fredzo/SarsatJRX/SarsatJRX-code/src/Beacon.cpp

#include "Beacon.h"
#include "Util.h"

// 21 bits BCH polynomial
#define BCH_21_POLYNOMIAL   0b1001101101100111100011UL 
#define BCH_21_POLY_LENGTH  22
// 12 bits BCH polynomial
#define BCH_12_POLYNOMIAL   0b1010100111001UL
#define BCH_12_POLY_LENGTH  13

// User
const Beacon::Protocol Beacon::Protocol::USER_EPIRB_MARITIME(Beacon::Protocol::Type::USER);
const Beacon::Protocol Beacon::Protocol::USER_EPIRB_RADIO(Beacon::Protocol::Type::USER);
const Beacon::Protocol Beacon::Protocol::USER_ELT(Beacon::Protocol::Type::USER);
const Beacon::Protocol Beacon::Protocol::USER_SERIAL(Beacon::Protocol::Type::USER);
const Beacon::Protocol Beacon::Protocol::USER_TEST(Beacon::Protocol::Type::USER);
const Beacon::Protocol Beacon::Protocol::USER_ORB(Beacon::Protocol::Type::USER);
const Beacon::Protocol Beacon::Protocol::USER_NAT(Beacon::Protocol::Type::USER);
const Beacon::Protocol Beacon::Protocol::USER_2G(Beacon::Protocol::Type::USER);
// Standard
const Beacon::Protocol Beacon::Protocol::STD_EPIRB(Beacon::Protocol::Type::STANDARD_LOCATION);
const Beacon::Protocol Beacon::Protocol::STD_ELT_24(Beacon::Protocol::Type::STANDARD_LOCATION);
const Beacon::Protocol Beacon::Protocol::STD_ELT_SERIAL(Beacon::Protocol::Type::STANDARD_LOCATION);
const Beacon::Protocol Beacon::Protocol::STD_ELT_AIRCRAFT(Beacon::Protocol::Type::STANDARD_LOCATION);
const Beacon::Protocol Beacon::Protocol::STD_EPIRB_SERIAL(Beacon::Protocol::Type::STANDARD_LOCATION);
const Beacon::Protocol Beacon::Protocol::STD_PLB_SERIAL(Beacon::Protocol::Type::STANDARD_LOCATION);
const Beacon::Protocol Beacon::Protocol::STD_SHIP(Beacon::Protocol::Type::STANDARD_LOCATION);
const Beacon::Protocol Beacon::Protocol::STD_TEST(Beacon::Protocol::Type::STANDARD_LOCATION);
// National
const Beacon::Protocol Beacon::Protocol::NAT_ELT(Beacon::Protocol::Type::NATIONAL_LOCATION);
const Beacon::Protocol Beacon::Protocol::NAT_EPIRB(Beacon::Protocol::Type::NATIONAL_LOCATION);
const Beacon::Protocol Beacon::Protocol::NAT_PLB(Beacon::Protocol::Type::NATIONAL_LOCATION);
const Beacon::Protocol Beacon::Protocol::NAT_TEST(Beacon::Protocol::Type::NATIONAL_LOCATION);
// RLS / ELT / Spare
const Beacon::Protocol Beacon::Protocol::RLS(Beacon::Protocol::Type::RLS_LOCATION);
const Beacon::Protocol Beacon::Protocol::ELT_DT(Beacon::Protocol::Type::ELT_DT_LOCATION);
const Beacon::Protocol Beacon::Protocol::SPARE(Beacon::Protocol::Type::SPARE);
const Beacon::Protocol Beacon::Protocol::UNKNOWN(Beacon::Protocol::Type::UNKNOWN);


String Beacon::Protocol::getTypeName(bool longFrame) const
{
    switch (type)
    {
        case Type::STANDARD_LOCATION:
            return F("Standard Protocol");
            break;
        case Type::NATIONAL_LOCATION:
            return F("National Protocol");
            break;
        case Type::RLS_LOCATION:
            return F("RLS");
            break;
        case Type::ELT_DT_LOCATION :
            return F("ELT(DT)");
            break;
        case Type::USER:
            return longFrame ? F("User Location Protocol") : F("User Protocol");
            break;
        case Type::SPARE:
            return F("Spare Protocol");
            break;
        case Type::UNKNOWN :
        default:
            return F("Unknown Protocol");
    }
}

uint64_t getBits(byte *data, int startBit, int endBit)
{
    uint64_t result = 0;
    // 0 bases bit count
    startBit--;
    int numBits = endBit - startBit;

    // get a pointer to the starting byte...
    const byte *pData = &(data[startBit / 8]);
    byte b = *pData;

    // calculate the starting bit within that byte...
    int bitOffset = 7 - (startBit % 8);

    // iterate for the desired number of bits...
    for(int i = 0; i < numBits; ++i)
    {
        // make room for the next bit...
        result <<= 1;
        // copy the bit...
        result |= ((b >> bitOffset) & 0x01);
        // reached the end of the current byte?
        if (--bitOffset < 0)
        {
            b = *(++pData); // go to the next byte...
            bitOffset = 7; // restart at the first bit in that byte...
        }
    }

    // all done...
    return result;
}

uint64_t computeBCH(byte* frame, int startBit, int endBit, unsigned long poly, int polyLength)
{   // Length of data to be checked (not including the BCH code)
    int dataLength = endBit-startBit+1;
    // Total lengh (including the BCH code that will be padded to zeros (BCH code length is polyLengh-1))
    int totalLength = dataLength+polyLength-1;
    // Start with the first polyLength bits
    uint64_t result = getBits(frame, startBit,startBit+polyLength-1);
#ifdef DEBUG_BCH    
    Serial.println("BCH calculation :");
    Serial.println((unsigned long)result,2);
#endif
    for (int i = polyLength; i <= totalLength; i++) 
    {   // Iterate on each bit after the first polyLength batch
        bool firstBit = result >> (polyLength-1);
#ifdef DEBUG_BCH    
        Serial.print("First bit :");
        Serial.println(firstBit,2);
#endif
        if(firstBit)
        {   // We have a leading 1 => xor the result with the poly
            result = result^poly;
#ifdef DEBUG_BCH    
            for(int j = 0; j < i-polyLength; j++) Serial.print(" ");
            Serial.println((unsigned long)result,2);
#endif
        }
        if(i<totalLength)
        {   // Move to next bit
            result = result << 1;
#ifdef DEBUG_BCH    
            for(int j = 0; j < i-polyLength; j++) Serial.print(" ");
            Serial.println((unsigned long)result,2);
#endif
            if(i<dataLength)
            {   // Append next bit
                result |= getBits(frame,startBit+i,startBit+i);
#ifdef DEBUG_BCH    
                for(int j = 0; j < i-polyLength; j++) Serial.print(" ");
                Serial.println((unsigned long)result,2);
#endif
            } // else : 0 padding after data length
        }
    }
    return result;
}

uint64_t computeBCH1(byte* frame)
{
    return computeBCH(frame,25,85,BCH_21_POLYNOMIAL,BCH_21_POLY_LENGTH);
}

uint64_t computeBCH2(byte* frame)
{
    return computeBCH(frame,107,132,BCH_12_POLYNOMIAL,BCH_12_POLY_LENGTH);
}

/**
 * Flip the specified bit in this beacon's data
 */
void Beacon::flipBit(int bit) {
    int byteIdx = (bit - 1) / 8;
    int bitIdx = 7 - ((bit - 1) % 8);
    frame[byteIdx] ^= (1 << bitIdx);
}

/**
 * Single bit error correction to match BCH1 or BCH2 code
 */
void Beacon::simpleCorrection(bool isBCH1) {
    for (int i = (isBCH1 ? 25 : 107); i <= (isBCH1 ? 85 : 132); i++) {
        flipBit(i);
        if ((isBCH1 ? (computeBCH1(frame) == bch1) : (computeBCH2(frame) == bch2))) {
            if (isBCH1) {
                computedBch1 = bch1;
                bch1Corrected = true;
            } else {
                computedBch2 = bch2;
                bch2Corrected = true;
            }
            break;
        }
        flipBit(i);  // Restore bit value
    }
}



Beacon::Beacon(volatile byte frameBuffer[], Rtc::Date date)
{   // Get a local copy of the original frame
    memcpy(frame,(const void*)frameBuffer,SIZE);
    Beacon::date = date;
    parseFrame();
}

String Beacon::getFrameTitle()
{
    if (frameMode == Beacon::FrameMode::SELF_TEST) 
    {  // Self-test message frame synchronisation byte
        return F("Self-test 406");
    }
    else if (frameMode == Beacon::FrameMode::NORMAL) 
    {   // Normal message frame synchronisation byte
        if(protocol == &Protocol::USER_SERIAL)
        {
            return F("Serial 406");
        }
        else if(protocol == &Protocol::USER_TEST)
        {
            return F("User Test 406");
        }
        else if(protocol == &Protocol::USER_ORB)
        {
            return F("Orbitography 406");
        }
        else if(protocol == &Protocol::USER_NAT)
        {
            return F("National 406");
        }
        else if(protocol == &Protocol::STD_TEST)
        {
            return F("Test Std. 406");
        }
        else if(protocol == &Protocol::NAT_TEST)
        {
            return F("Test Nat. 406");
        }
        else if(protocol == &Protocol::SPARE)
        {
            return F("Spare 406");
        }
        else
        {
            return F("Distress 406");
        }
    }
    else
    {   // Unknown frame format
        return F("Unknown 406");
    }
}

String Beacon::getProtocolName()
{
    return protocol->getTypeName(longFrame);
}

String Beacon::getProtocolDesciption()
{
    // User
    if(protocol == &Protocol::USER_EPIRB_MARITIME)
    {
        return F("EPIRB - Maritime");
    }
    else if(protocol == &Protocol::USER_EPIRB_RADIO)
    {
        return F("EPIRB - Radio Call Sign");
    }
    else if(protocol == &Protocol::USER_ELT)
    {
        return F("ELT - Aviation");
    }
    else if(protocol == &Protocol::USER_SERIAL)
    {
        return F("Serial User Protocol");
    }
    else if(protocol == &Protocol::USER_TEST)
    {
        return F("Test User Protocol");
    }
    else if(protocol == &Protocol::USER_ORB)
    {
        return F("Orbitography Protocol");
    }
    else if(protocol == &Protocol::USER_NAT)
    {
        return F("National User Protocol");
    }
    else if(protocol == &Protocol::USER_2G)
    {
        return F("2nd Generation Beacons");
    }
    // Standard
    else if(protocol == &Protocol::STD_EPIRB)
    {
        return F("EPIRB - MMSI / Location");
    }
    else if(protocol == &Protocol::STD_ELT_24)
    {
        return F("ELT-24-bit Address / Location");
    }
    else if(protocol == &Protocol::STD_ELT_SERIAL)
    {
        return F("ELT Serial Location");
    }
    else if(protocol == &Protocol::STD_ELT_AIRCRAFT)
    {
        return F("ELT Serial Aircradt Location");
    }
    else if(protocol == &Protocol::STD_EPIRB_SERIAL)
    {
        return F("EPIRB Serial Location");
    }
    else if(protocol == &Protocol::STD_PLB_SERIAL)
    {
        return F("PLB Serial Location");
    }
    else if(protocol == &Protocol::STD_SHIP)
    {
        return F("Ship Security Location");
    }
    else if(protocol == &Protocol::STD_TEST)
    {
        return F("Test Standard Location");
    }
    // National
    else if(protocol == &Protocol::NAT_ELT)
    {
        return F("ELT National Location");
    }
    else if(protocol == &Protocol::NAT_EPIRB)
    {
        return F("EPIRB National Location");
    }
    else if(protocol == &Protocol::NAT_PLB)
    {
        return F("PLB National Location");
    }
    else if(protocol == &Protocol::NAT_TEST)
    {
        return F("Test National Location");
    }
    // RLS / ELT / Spare
    else if(protocol == &Protocol::RLS)
    {
        return F("RLS Location Protocol");
    }
    else if(protocol == &Protocol::ELT_DT)
    {
        return F("ELT(DT) Location Protocol");
    }
    else if(protocol == &Protocol::SPARE)
    {
        return F("Spare");
    }
    else
    {
        return F("Unknown Protocol");
    }
}

bool Beacon::hasMainLocatingDevice()
{
    return (mainLocatingDevice != MainLocatingDevice::UNDEFINED);
}

String Beacon::getMainLocatingDeviceName()
{
    switch (mainLocatingDevice)
    {
        case MainLocatingDevice::EXTERNAL_NAV :
            return F("Exernal");
            break;
        case MainLocatingDevice::INTERNAL_NAV :
            return F("Internal");
            break;
        default:
            return F("Undefined");
    }
}

bool Beacon::hasAuxLocatingDevice()
{
    return (auxLocatingDevice != AuxLocatingDevice::UNDEFINED);
}

String Beacon::getAuxLocatingDeviceName()
{
    switch (auxLocatingDevice)
    {
        case AuxLocatingDevice::NONE :
            return F("No device");
            break;
        case AuxLocatingDevice::NONE_OR_OTHER :
            return F("Other or no device");
            break;
        case AuxLocatingDevice::OTHER :
            return F("Other device");
            break;
        case AuxLocatingDevice::MHZ121_5 :
            return F("121.5 MHz");
            break;
        case AuxLocatingDevice::SART :
            return F("Maritime locating: 9 GHz SART");
            break;
        default:
            return F("Undefined");
    }
}

void Beacon::parseProtocol()
{
    protocolFlag = getBits(frame,26,26); // protocol flag : bit 26
    if(protocolFlag)
    {   // User protocol
        protocolCode = getBits(frame,37,39);  // protocol code : bits 37-39
    }
    else
    {   // Other protocols
        protocolCode = getBits(frame,37,40);    // protocol code     bits 37-40
    }

    if(!longFrame || protocolFlag == 1) 
    {   // User protocol (3 bits)
        switch(protocolCode)
        {
            case 0b000 :
                protocol = &Protocol::USER_ORB;
                break;
            case 0b001 :
                protocol = &Protocol::USER_ELT;
                break;
            case 0b010 :
                protocol = &Protocol::USER_EPIRB_MARITIME;
                isMaritime = true;
                break;
            case 0b011 :
                protocol = &Protocol::USER_SERIAL;
                break;
            case 0b100 :
                protocol = &Protocol::USER_NAT;
                break;
            case 0b101 :
                protocol = &Protocol::USER_2G;
                break;
            case 0b110 :
                protocol = &Protocol::USER_EPIRB_RADIO;
                isMaritime = true;
                break;
            case 0b111 :
                protocol = &Protocol::USER_TEST;
                break;
            default:
                protocol = &Protocol::UNKNOWN;
        }
    }
    else
    {   // Other protocols (4 bits)
        switch(protocolCode)
        {
            case 0b0000 :
            case 0b0001 :
                protocol = &Protocol::SPARE;
                break;
            case 0b0010 :
                protocol = &Protocol::STD_EPIRB;
                break;
            case 0b0011 :
                protocol = &Protocol::STD_ELT_24;
                break;
            case 0b0100 :
                protocol = &Protocol::STD_ELT_SERIAL;
                break;
            case 0b0101 :
                protocol = &Protocol::STD_ELT_AIRCRAFT;
                break;
            case 0b0110 :
                protocol = &Protocol::STD_EPIRB_SERIAL;
                break;
            case 0b0111 :
                protocol = &Protocol::STD_PLB_SERIAL;
                break;
            case 0b1000 :
                protocol = &Protocol::NAT_ELT;
                break;
            case 0b1001 :
                protocol = &Protocol::ELT_DT;
                break;
            case 0b1010 :
                protocol = &Protocol::NAT_EPIRB;
                break;
            case 0b1011 :
                protocol = &Protocol::NAT_PLB;
                break;
            case 0b1100 :
                protocol = &Protocol::STD_SHIP;
                break;
            case 0b1101 :
                protocol = &Protocol::RLS;
                break;
            case 0b1110 :
                protocol = &Protocol::STD_TEST;
                break;
            case 0b1111 :
                protocol = &Protocol::NAT_TEST;
                break;
            default:
                protocol = &Protocol::UNKNOWN;
        }
    }
}

void Beacon::setSerialNumber(uint32_t serial)
{
        serialNumber  = String(serial, HEX);
        serialNumber.toUpperCase();
        serialNumber = String(serial,DEC) + " (0x" + serialNumber + ")";
}

void Beacon::parseAdditionalData()
{
    hasAdditionalData = false;
    hasSerialNumber = false;
    if(protocolFlag)
    {   // User protocols
        if(protocolCode == 0b011)
        {   // Serial user
            byte serialUserProtocol = getBits(frame,40, 42);
            hasAdditionalData = true;
            switch(serialUserProtocol)
            {
                case 0b000: additionalData  = F("ELTs/serial identification number"); break;
                case 0b001: additionalData  = F("ELTs/aircraft operator & serial #"); break;
                case 0b010: additionalData  = F("Float free EPIRBs/serial #"); isMaritime = true; break;
                case 0b011: additionalData  = F("ELTs with aircraft 24-bit address"); break;
                case 0b100: additionalData  = F("Non float free EPIRBs/serial #"); break;
                case 0b110: additionalData  = F("PLBs/serial identification #"); break;
                default : hasAdditionalData = false;
            }
            hasSerialNumber = true;
            setSerialNumber((serialUserProtocol == 0b011) ? getBits(frame, 44, 67) : (serialUserProtocol == 0b001) ? getBits(frame, 62, 73) : getBits(frame, 44, 63));
        }
        if (!longFrame) {
            hasEmergency = getBits(frame, 107, 107);
            if (hasEmergency) {
                isAutoamticEmergency = getBits(frame, 108, 108);
                if (isMaritime) {
                    uint8_t emmergency = getBits(frame, 109, 112);
                    switch (emmergency) {
                        case 0b0001: emergencyType = F("Fire/explosion"); break;
                        case 0b0010: emergencyType = F("Flooding"); break;
                        case 0b0011: emergencyType = F("Collision"); break;
                        case 0b0100: emergencyType = F("Grounding"); break;
                        case 0b0101: emergencyType = F("Danger of capsizing"); break;
                        case 0b0110: emergencyType = F("Sinking"); break;
                        case 0b0111: emergencyType = F("Disabled and adrift"); break;
                        case 0b1000: emergencyType = F("Abandoning ship"); break;
                        default:     emergencyType = F("Unspecified distress");
                    }
                } else {
                    bool fire = getBits(frame, 109, 109);
                    bool med = getBits(frame, 110, 110);
                    bool disabled = getBits(frame, 111, 111);
                    if (fire) emergencyType = "Fire";
                    if (med) {
                        if (fire) emergencyType += "+";
                        emergencyType += "Medical";
                    }
                    if (disabled) {
                        if (fire || med) emergencyType += "+";
                        emergencyType += "Disabled";
                    }
                }
            }
        }
    }
    else if (longFrame)
    {   // Long frame other than User Protocol
        switch(protocolCode)
        {
            case 0b0010 :
                {
                hasSerialNumber = true;
                setSerialNumber(getBits(frame,61,64));
                }
                break;
            case 0b1100 :
                {
                hasAdditionalData = true;
                uint32_t mmsi = getBits(frame,41,60);
                additionalData = "MMSI=" + String(mmsi, HEX) + " MID=" + mmsi;
                additionalData.toUpperCase();
                }
                break;
            case 0b0011 :
                {
                hasAdditionalData = true;
                hasSerialNumber = true;
                setSerialNumber(getBits(frame,41,64));
                additionalData = "24 bits aircraft address";
                }
                break;
            case 0b0100 :
            case 0b0110 :
            case 0b0111 :
                {
                hasAdditionalData = true;
                hasSerialNumber = true;
                uint32_t csTaNumber = getBits(frame,41, 50);
                additionalData = "C/S TA #=" + String(csTaNumber, DEC);
                setSerialNumber(getBits(frame,51, 64));
                }
                break;
            case 0b0101 :
                { 
                hasAdditionalData = true;
                hasSerialNumber = true;
                uint32_t data = getBits(frame,41, 45); // 1st char
                data = data + 32;
                additionalData = BAUDOT_CODE[data];

                data = getBits(frame,46, 50); // 2nd char
                data = data + 32;
                additionalData = additionalData + BAUDOT_CODE[data];

                data = getBits(frame,51, 55); // 3rd char
                data = data + 32;
                additionalData = additionalData + BAUDOT_CODE[data];

                additionalData = "Op Design.=" + additionalData;

                setSerialNumber(getBits(frame,56, 64));
                }
                break;
            case 0b1000 :
            case 0b1010 :
            case 0b1011 :
            case 0b1111 :
                {
                hasSerialNumber = true;
                hasAdditionalData = true;
                setSerialNumber(getBits(frame,41, 58));
                uint32_t natNum = getBits(frame,127, 132);
                additionalData = "National data=" + String(natNum, DEC);
                }
                break;
        }
    }
}

void Beacon::parseLocatingDevices()
{
    // Main 
    bool mainLocating;
    if(protocol->isStandard() || protocol->isNational())
    {
        mainLocating = getBits(frame,111,111);
        mainLocatingDevice = mainLocating ? MainLocatingDevice::INTERNAL_NAV : MainLocatingDevice::EXTERNAL_NAV;
    }
    else if (protocol->isUser()||protocol->isRls())
    {
        mainLocating = getBits(frame,107,107);
        mainLocatingDevice = mainLocating ? MainLocatingDevice::INTERNAL_NAV : MainLocatingDevice::EXTERNAL_NAV;
    }
    // Aux
    if(protocol->isStandard() || protocol->isNational())
    {
        bool auxLocating = getBits(frame,112,112);
        auxLocatingDevice = auxLocating ? AuxLocatingDevice::MHZ121_5 : AuxLocatingDevice::NONE_OR_OTHER;
    }
    else if (protocol->isRls())
    {
        bool auxLocating = getBits(frame,108,108);
        auxLocatingDevice = auxLocating ? AuxLocatingDevice::MHZ121_5 : AuxLocatingDevice::NONE_OR_OTHER;
    }
    else if (protocol->isUser() && protocolCode != 0b100)
    {   // User protocol with an aux locating device
        byte auxLocating = getBits(frame,84,85);
        switch (auxLocating)
        {
            case 0b00:
                auxLocatingDevice = AuxLocatingDevice::NONE;
                break;
            case 0b01:
                auxLocatingDevice = AuxLocatingDevice::MHZ121_5;
                break;
            case 0b10:
                auxLocatingDevice = AuxLocatingDevice::SART;
                break;
            case 0b11:
                auxLocatingDevice = AuxLocatingDevice::OTHER;
                break;
        }
    }
}

void Beacon::parseFrame()
{
    long latofmin, latofsec, lonofmin, lonofsec;
    bool latoffset, lonoffset;

    longFrame = getBits(frame,25,25);       // frame size : bit 25
    parseProtocol();
    unsigned long countryCode = getBits(frame, 27,36); // country code bit 27-36
    country = Country::getCountry(countryCode);
        
    if (frame[2] == 0xD0) 
    {  // Self-test message frame synchronisation byte
        frameMode = FrameMode::SELF_TEST;
    }
    else if (frame[2] == 0x2F) 
    { // Normal message frame synchronisation byte
        frameMode = FrameMode::NORMAL;
    }
    else
    {
        frameMode = FrameMode::UNKNOWN;
    }

    if (longFrame)
    {
        if(protocol->isUser() && !isOrbito()) 
        {   // User loc protocol long frame (no location for Obitography frame)
            location.latitude.orientation = (frame[13] & 0x10) >> 4;   
            location.latitude.degrees = ((frame[13] & 0x0F) << 3 | (frame[14] & 0xE0) >> 5);
            location.latitude.minutes = (frame[14] & 0x1E) >> 1;
            location.latitude.minutes = (location.latitude.minutes * 4);
            location.longitude.orientation = (frame[14] & 0x01);           
            location.longitude.degrees = (frame[15]);
            location.longitude.minutes = (frame[16] & 0xF0) >> 4;
            location.longitude.minutes = (location.longitude.minutes * 4);
        }
        else if(protocol->isNational())
        {   // Nat loc protocol
            latoffset = (frame[14] & 0x80) >> 7;   // Latitude NAT LOCATION
            location.latitude.orientation = (frame[7] & 0x20) >> 5;   
            location.latitude.degrees = ((frame[7] & 0x1F) << 2 | (frame[8] & 0xC0) >> 6);
            location.latitude.minutes = (frame[8] & 0x3E) >> 1;
            location.latitude.minutes = (location.latitude.minutes * 2);
            latofmin = (frame[14] & 0x60) >> 5;
            latofsec = (frame[14] & 0x1E) >> 1;
            latofsec = (latofsec * 4);
            if (latoffset == 1) 
            {
                location.latitude.minutes += latofmin;
                location.latitude.seconds += latofsec;
            }
            else if (latoffset == 0) 
            {
                location.latitude.minutes -= latofmin;
                if (location.latitude.minutes < 0) 
                {
                    location.latitude.minutes += 60;
                    location.latitude.degrees -= 1;
                }
                location.latitude.seconds -= latofsec;
                if (location.latitude.seconds < 0) 
                {
                    location.latitude.seconds += 60;
                    location.latitude.minutes -= 1;
                }
            }

            lonoffset = (frame[14] & 0x01);
            location.longitude.orientation = (frame[8] & 0x01);           
            location.longitude.degrees = (frame[9]);
            location.longitude.minutes = (frame[10] & 0xF8) >> 3;
            location.longitude.minutes = (location.longitude.minutes * 2);
            lonofmin = (frame[15] & 0xC0) >> 6;
            lonofsec = (frame[15] & 0x3C) >> 2;
            lonofsec = (lonofsec * 4);
            if (lonoffset == 1) 
            {
                location.longitude.minutes += lonofmin;
                location.longitude.seconds += lonofsec;
            }
            else if (lonoffset == 0) 
            {
                location.longitude.minutes -= lonofmin;
                if (location.longitude.minutes < 0) 
                {
                    location.longitude.minutes += 60;
                    location.longitude.degrees -= 1;
                }
                location.longitude.seconds -= lonofsec;
                if (location.longitude.seconds < 0) 
                {
                    location.longitude.seconds += 60;
                    location.longitude.minutes -= 1;
                }
            }
        }
        else if (protocol->isStandard())
        {   //Std loc protocol
            latoffset = (frame[14] & 0x80) >> 7;
            location.latitude.orientation = (frame[8] & 0x80) >> 7; 
            location.latitude.degrees = (frame[8] & 0x7F);
            location.latitude.minutes = (frame[9] & 0xC0) >> 6;
            location.latitude.minutes = (location.latitude.minutes * 15);
            latofmin = (frame[14] & 0x7C) >> 2;
            latofsec = ((frame[14] & 0x03) << 2 | (frame[15] & 0xC0) >> 6);
            latofsec = (latofsec * 4);
            if (latoffset == 1) 
            {
                location.latitude.minutes += latofmin;
                location.latitude.seconds += latofsec;
            }
            else if (latoffset == 0) 
            {
                location.latitude.minutes -= latofmin;
                if (location.latitude.minutes < 0) 
                {
                    location.latitude.minutes += 60;
                    location.latitude.degrees -= 1;
                }
                location.latitude.seconds -= latofsec;
                if (location.latitude.seconds < 0) 
                {
                    location.latitude.seconds += 60;
                    location.latitude.minutes -= 1;
                }
            }
            
            lonoffset = (frame[15] & 0x20) >> 5;  //Longitude STD LOCATION
            location.longitude.orientation = (frame[9] & 0x20) >> 5; 
            location.longitude.degrees = ((frame[9] & 0x1F) << 3 | (frame[10] & 0xE0) >> 5);
            location.longitude.minutes = (frame[10] & 0x18) >> 3;
            location.longitude.minutes = (location.longitude.minutes * 15);
            lonofmin = (frame[15] & 0x1F);
            lonofsec = (frame[16] & 0xF0) >> 4;
            lonofsec = (lonofsec * 4);
            if (lonoffset == 1) 
            {
                location.longitude.minutes += lonofmin;
                location.longitude.seconds += lonofsec;
            }
            else if (lonoffset == 0) 
            {
                location.longitude.minutes -= lonofmin;
                if (location.longitude.minutes < 0) 
                {
                    location.longitude.minutes += 60;
                    location.longitude.degrees -= 1;
                }
                location.longitude.seconds -= lonofsec;
                if (location.longitude.seconds < 0) 
                {
                    location.longitude.seconds += 60;
                    location.longitude.minutes -= 1;
                }
            }
        }
        else if(protocol->isRlsOrElt())
        {   // RLS Location protocol => protocolCode == 0b1101 / ELT(DT) Location protocol => protocolCode == 0b1001
            latoffset = (frame[14] & 0x20) >> 5;
            location.latitude.orientation = (frame[8] & 0x20) >> 5; 
            location.latitude.degrees = ((frame[8] & 0x1F) << 2) | ((frame[9] & 0xC0) >> 6);
            location.latitude.minutes = (frame[9] & 0x20) >> 5;
            location.latitude.minutes = (location.latitude.minutes * 30);
            latofmin = (frame[14] & 0x1E) >> 1;
            latofsec = ((frame[14] & 0x01) << 3 | (frame[15] & 0xE0) >> 5);
            latofsec = (latofsec * 4);
            if (latoffset == 1) 
            {
                location.latitude.minutes += latofmin;
                location.latitude.seconds += latofsec;
            }
            else if (latoffset == 0) 
            {
                location.latitude.minutes -= latofmin;
                if (location.latitude.minutes < 0) 
                {
                    location.latitude.minutes += 60;
                    location.latitude.degrees -= 1;
                }
                location.latitude.seconds -= latofsec;
                if (location.latitude.seconds < 0) 
                {
                    location.latitude.seconds += 60;
                    location.latitude.minutes -= 1;
                }
            }
            
            lonoffset = (frame[15] & 0x10) >> 4;
            location.longitude.orientation = (frame[9] & 0x10) >> 4; 
            location.longitude.degrees = ((frame[9] & 0x0F) << 4 | (frame[10] & 0xF0) >> 4);
            location.longitude.minutes = (frame[10] & 0x08) >> 3;
            location.longitude.minutes = (location.longitude.minutes * 30);
            lonofmin = (frame[15] & 0x0F);
            lonofsec = (frame[16] & 0xF0) >> 4;
            lonofsec = (lonofsec * 4);
            if (lonoffset == 1) 
            {
                location.longitude.minutes += lonofmin;
                location.longitude.seconds += lonofsec;
            }
            else if (lonoffset == 0) 
            {
                location.longitude.minutes -= lonofmin;
                if (location.longitude.minutes < 0) 
                {
                    location.longitude.minutes += 60;
                    location.longitude.degrees -= 1;
                }
                location.longitude.seconds -= lonofsec;
                if (location.longitude.seconds < 0) 
                {
                    location.longitude.seconds += 60;
                    location.longitude.minutes -= 1;
                }
            }
        }
    }

    // Parse additional data
    parseAdditionalData();

    // Parse locating device information
    parseLocatingDevices();

    // Hex id from bits 26-85
    identifier = getBits(frame,26,85);

    uint32_t hexIdHigh = (uint32_t)(identifier >> 32);
    uint32_t hexIdLow = (uint32_t)identifier;

    if (protocol->isStandard()) {
        // default value of bits 65 to 74 = 0 111111111 / default value of bits 75 to 85 = 0 1111111111
        hexIdLow &= 0b11111111111000000000000000000000;
        hexIdLow |= 0b00000000000011111111101111111111;
    } else if (protocol->isNational()) {
        // default value of bits 59 to 71 = 0 1111111 00000 / default value of bits 72 to 85 = 0 11111111 00000
        hexIdLow &= 0b11111000000000000000000000000000;
        hexIdLow |= 0b00000011111110000001111111100000;
    } else if (protocol->isRlsOrElt()) {
        // default value of bits 67 to 75 = 0 11111111 / default value of bits 76 to 85 = 0 111111111
        hexIdLow &= 0b11111111111110000000000000000000;
        hexIdLow |= 0b00000000000000111111110111111111;
    }
    // Format HexId to string
    char buffer[32];
    snprintf(buffer,sizeof(buffer),"%07lX%08lX",hexIdHigh,hexIdLow);
    hexId = String(buffer);

    // Check for Empty frame
    if(isOrbito()&&!longFrame)
    {
        isEmpty = true;
        for (size_t i = 3; i < SIZE; i++) 
        {
            if (frame[i] != 0) 
            {
                isEmpty = false;
                break;
            }
        }
    }
    else
    {
        isEmpty = false;
    }

    // Actual and computed BCH1 and BCH2 values
    bch1 = getBits(frame,86,106);
    computedBch1 = computeBCH1(frame);
    // Try and correct single bit error on  BCH1 (bits 25-85)
    if (computedBch1 != bch1) {
        simpleCorrection(true);
    }

    // Special handing of Orbitography Protocol that has no BCH2 error correction code
    hasBch2 = longFrame && !isOrbito();
    if(hasBch2)
    {
        bch2 = getBits(frame,133,144);
        computedBch2 = computeBCH2(frame);
        // Try and correct single bit error on  BCH2 (bits 107 - 132)
        if (computedBch2 != bch2) {
            simpleCorrection(false);
        }
    }
    static bool isCorrecting = false;
    // If BCH1 or BCH2 has been corrected, we need to parse frame again to update beacon properties
    if (!isCorrecting && (bch1Corrected || bch2Corrected)) {
        // Prevent recursion
        isCorrecting = true;
        parseFrame();
        isCorrecting = false;
    }
}

bool Beacon::isBch1Valid()
{
    return (bch1 == computedBch1);
}

bool Beacon::isBch2Valid()
{
    return (bch2 == computedBch2);
}

bool Beacon::isFrameValid()
{
    return isBch1Valid() && ((!hasBch2)||isBch2Valid()) && (!isEmpty);
}

bool Beacon::isOrbito()
{
    return (protocol == &Protocol::USER_ORB);    
}

String Beacon::toKvpString()
{
    String result;
    result+="date="+date.getDateString()+"\n";
    result+="time="+date.getTimeString()+"\n";
    // Frame title
    result+="title="+getFrameTitle()+"\n";
    // Protocol name
    result+="protocol="+getProtocolName()+"\n";
    // Protocol description
    result+="protocolDesc="+getProtocolDesciption()+"\n";
    // Protocol additional data
    if(hasAdditionalData)
    {   // Additionnal protocol data
        result+="protocolAddData="+additionalData+"\n";
    }

    // Location
    // Country
    result+="country="+country.toString()+"\n";
    // Coordinates
    if(!location.isUnknown())
    {
        result+="lat="+String(location.latitude.getFloatValue(),6)+"\n";
        result+="lon="+String(location.longitude.getFloatValue(),6)+"\n";
    }
    // Control codes
    result+="bch1=" + (isBch1Valid() ? (bch1Corrected ? String("co") : String("ok")) : String("ko")) +"\n";
    if(longFrame && hasBch2) 
    {   // No second proteced field in short frames
        result+="bch2=" + (isBch2Valid() ? (bch2Corrected ? String("co") : String("ok")) : String("ko")) +"\n";
    }

    // Hex ID
    result+="hexId=" + hexId +"\n";

    // Serial #
    if(hasSerialNumber)
    { // Serial number
        result+="serial=" + serialNumber +"\n";
    }

    // Emergency
    if(hasEmergency)
    { // Serial number
        result+="emergency=" + emergencyType +"\n";
        result+="emergencyMode=" + (isAutoamticEmergency ? String("auto") : String("manual")) +"\n";
    }

    // Location devices
    if(hasMainLocatingDevice())
    { // Main locating device
        result+="mainDevice=" + getMainLocatingDeviceName() +"\n";
    }

    if(hasAuxLocatingDevice())
    {   // Auxiliary locating device
        result+="auxDevice=" + getAuxLocatingDeviceName() +"\n";
    }

    // Data
    result+="data=" + hexString(false) +"\n";
    return result;
}

String Beacon::hexString(bool withHeader)
{
    return toHexString(frame, false, (withHeader ? 0 : 3), (longFrame ? 18 : 14));
}
