fredzo/SarsatJRX/SarsatJRX-code/src/Power.cpp

#include "Power.h"
#include <SarsatJRXConf.h>
#include <Util.h>

#define MAX_BATTERY_VOLTAGE_DOWN    4.1
#define MAX_BATTERY_VOLTAGE_UP      4.2
#define POWER_SAMPLE_PERIOD         200  // 200ms
#define POWER_UPDATE_PERIOD         1000 // 1s
#define CHARGE_SAMPLE_PERIOD        1    // 1 ms: depending on charger chip mode, fickering is charge pin going low for around 1ms every 10 to 50 ms 
#define CHARGE_SAMPLE_COUNT         100  // Wait for 100 consecutive samples with same value to validate charge state
#define CHARGE_BATTERY_OFF_COUNT    10   // Wait for 10 state changes to determine if battery is off

// Static members
Power *Power::powerInstance = nullptr;


void Power::powerInit()
{
  pinMode(BATTERY_ADC_PIN, ANALOG);      // Battery level pin
  pinMode(CHARGE_INPUT_PIN, INPUT_PULLUP);      // Charge status pin
}


/**
 * @brief Returns actual VCC value
 * 
 * @return VCC value
 */
float Power::getVccValue() {
    changed = false;
    return powerValue;
}

/**
 * @brief Read VCC value into the provided char* with the format "x.xx"
 * 
 * @return The VCC string value
 */
String Power::getVccStringValue()
{   /* 6 is mininum width, 4 is precision; float value is copied onto angleStr */
    char buffer[8];
    dtostrf(getVccValue(), 3, 2, buffer);
    return (String(buffer) + "V");
}

/**
 * @brief Read raw VCC value into the provided char* with the format "x.xx"
 * 
 * @return The VCC string value
 */
String Power::getRawVccStringValue()
{   /* 6 is mininum width, 4 is precision; float value is copied onto angleStr */
    char buffer[8];
    dtostrf(getRawVccValue(), 3, 2, buffer);
    return (String(buffer) + "V");
}

Power::PowerState Power::getPowerState()
{
    return state;
}

String Power::getPowerStateString()
{
    String result;
    switch (getPowerState())
    {
    case PowerState::FULL :
        result = "Battery full";
        break;
    case PowerState::ON_BATTERY :
        result = "On Battery";
        break;
    case PowerState::NO_BATTERY :
        result = "Battery switch off";
        break;
    case PowerState::CHARGING :
    default:
        result = "Charging";
        break;
    }
    return result;
}

bool Power::hasPowerStateChanged()
{
    bool result = powerStateChanged;
    powerStateChanged = false;
    return result;
}


int Power::getBatteryPercentage()
{
    return batteryPercentage;
}

// For rolling average
void Power::addPowerSample(float newVoltage) 
{
    if (voltageCount < BATTERY_BUFFER_SIZE) 
    {
        // Initial filling
        voltageBuffer[voltageIndex] = newVoltage;
        voltageSum += newVoltage;
        voltageCount++;
    } 
    else 
    {   // Buffer full : remove old value, add new
        float oldVoltage = voltageBuffer[voltageIndex];
        voltageBuffer[voltageIndex] = newVoltage;
        voltageSum += newVoltage - oldVoltage;
    }
    voltageIndex = (voltageIndex + 1) % BATTERY_BUFFER_SIZE;
}

// Get rolling average
float Power::getAveragePowerValue(void) 
{
    if (voltageCount == 0) return 0.0f;
    return voltageSum / voltageCount;
}

// Power task processing
void Power::handleTask()
{   // This task is in charge of updating power value and power state
    unsigned long now = millis();
    if(now - lastPowerSampleTime > POWER_SAMPLE_PERIOD)
    {   // Time to make a new sample
        lastPowerSampleTime = now;
        uint32_t v = analogReadMilliVolts(BATTERY_ADC_PIN);
        rawPowerValue = (((float)v)*2.0/1000.0);

        // Compute rolling average
        addPowerSample(rawPowerValue);
        float newValue = getAveragePowerValue();
        // Simu
        /* newValue = powerValue - 0.05;
        if(newValue < 3.3)
        {
            newValue = 4.3;
        }*/
        // Simu
        if((powerValue == 0) || (now - lastPowerUpdateTime > POWER_UPDATE_PERIOD))
        {
            lastPowerUpdateTime = now;
            if(abs(newValue - powerValue) > 0.01)
            {   // Filter small value changes
                powerValue = newValue;
                int newBatteryPercentage = voltageToPercent(powerValue,3.0f,4.0f);
                if(abs(newBatteryPercentage - batteryPercentage) > 5)
                {   // Round to nearest 5
                    batteryPercentage = ((newBatteryPercentage + 2) / 5) * 5;
                }
                changed = true;
            }
        }
    }
    if(now - lastChargeSampleTime > CHARGE_SAMPLE_PERIOD)
    {   // Time to make a new sample
        lastChargeSampleTime = now;
        int newValue = digitalRead(CHARGE_INPUT_PIN);
        if(newValue == lastChargeValue)
        {   // Is pin value stable (we want to detect the fickering state of the charging led of the TP4054 that refects no battery is connected (battery switch is off))
            if((chargeValueCount < CHARGE_SAMPLE_COUNT) || changed) // If power value changed, we may need to update state too
            {   // Count consecutive values
                chargeValueCount++;
                if(chargeValueCount >= CHARGE_SAMPLE_COUNT)
                {   // Update power state if value is stable
                    PowerState newState;
                    if(lastChargeValue)
                    {   // Led off (pin high) => either full or on battery
                        if(powerValue >= MAX_BATTERY_VOLTAGE_UP)
                        {
                            newState = PowerState::FULL;
                        }
                        else
                        {
                            if(powerValue >= MAX_BATTERY_VOLTAGE_DOWN && state == PowerState::CHARGING)
                            {   // Previous state was charging => must be full now
                                newState = PowerState::FULL;
                            }
                            else
                            {
                                newState = PowerState::ON_BATTERY;
                            }
                        }
                    }
                    else
                    {   // Charging
                        newState = PowerState::CHARGING;
                    }
                    if(newState != state)
                    {
                        state = newState;
                        changed = true;
                        powerStateChanged = true;
                    }
                }
            }
        }
        else
        {   // Led is flickering => no battery connected
            chargeValueCount = 0;
            if(state != PowerState::NO_BATTERY)
            {
                if(chargeSampleCount >= CHARGE_BATTERY_OFF_COUNT)
                {
                    state = PowerState::NO_BATTERY;
                    powerStateChanged = true;
                    changed = true;
                    chargeSampleCount = 0;
                }
                else
                {
                    chargeSampleCount++;
                }
            }
            lastChargeValue = newValue;
        }
    }
}
