fredzo/SarsatJRX/SarsatJRX-code/src/SoundManager.h

#ifndef MUSIC_MANAGER_H
#define MUSIC_MANAGER_H

#include <SarsatJRXConf.h>
#include <melody_player.h>
#include <melody_factory.h>


class SoundManager
{
    public :

        static SoundManager *getSoundManager()
        {
            if (soundManagerInstance == nullptr) {
                soundManagerInstance = new SoundManager();
            }
            return soundManagerInstance;
        }

        void init();

        void setVolume(byte volume);

        void playFrameSound(bool error);

        void playInvalidFrameSound();

        void playFilteredFrameSound();

        void playCountDownLowSound();

        void playCountDownHighSound();

        void playTouchSound();

        void unmute();


    private :

        MelodyPlayer* player;

        Melody frameOkSound;
        Melody frameKoSound;
        Melody frameInvalidSound;
        Melody frameFilteredSound;
        Melody countDownLowSound;
        Melody countDownHighSound;
        Melody touchSound;


        SoundManager()
        {   // Uses channel 4 since channel 0 is used for LCD Backlight
            player = new MelodyPlayer(BUZZER_PIN,4,LOW);
        };

        ~SoundManager()
        {
            delete player;
        };

        static SoundManager *soundManagerInstance;
};

#endif 
