fredzo/SarsatJRX/SarsatJRX-code/src/Util.cpp

#include "Util.h"


#ifdef DEBUG_RAM
uint32_t freeRam()
{
  return ESP.getFreeHeap();
}
void logFreeRam()
{
   Serial.printf("Free ram : %d\n",ESP.getFreeHeap());
}
#endif


/**
 * @brief Convert the provided frame to it's Hex String representation
 * 
 * @param frame the frame to convert
 * @param withSpace true if bytes should be seperated by spaces
 * @param start start byte
 * @param end end byte
 * @return String 
 */
String toHexString(volatile byte* frame, bool withSpace, int start, int end)
{
  char buffer[4];
  String result = "";
  for ( byte i = start; i < end; i++) 
  {
    snprintf(buffer,sizeof(buffer), "%02X", frame[i]);
    if(withSpace && i>start) 
    {
      result += " ";
    }
    result += buffer;
  }
  return result;
}

/**
 * @brief Read the provided hexString and store the content in the buffer
 * 
 * @param buffer the buffer to store the converted hex bytes into (the size must match the hex string size)
 * @param hexString the hex string to read
 */
void readHexString(volatile byte* buffer, String hexString) 
{
  for (unsigned int i = 0; i < hexString.length(); i += 2) {
    String byteString = hexString.substring(i, i+2);
    byte b = (byte)strtol(byteString.c_str(), NULL, 16);
    buffer[i/2]=b;
  }
}

String formatMemoryValue(uint32_t value, bool showByteValue)
{
  char buffer[64];
  uint32_t kbValue = value / 1024;
  if(showByteValue)
  {
    snprintf(buffer,sizeof(buffer),"%'d kB (%'d bytes)",kbValue,value);
  }
  else
  {
    snprintf(buffer,sizeof(buffer),"%'d kB",kbValue);
  }
  return String(buffer);
}

String formatFrequencyValue(uint32_t value)
{
  return (String(value) + " Mhz");
}

String formatDbmValue(int8_t value)
{
  return (String(value) + " dBm");
}

String formatHzFrequencyValue(uint32_t value)
{
  return (String(value/1000000) + " Mhz");
}

String formatSketchInformation(uint32_t size, String md5)
{
  int md5Length = md5.length();
  //Serial.println(md5);
  if(md5Length > 16)
  {
    md5 = md5.substring(0,8) + "..." + md5.substring(md5Length-8,md5Length);
    //Serial.println(md5);
  }
  return formatMemoryValue(size,false) + " (MD5=" + md5 + ")";
}

void formatBeaconFileName(char* buffer, size_t size, String name)
{
  snprintf(buffer,size,"%s/%s/%s - %s:%s:%s",name.substring(0,2),name.substring(2,4),name.substring(4,8),name.substring(9,11),name.substring(11,13),name.substring(13,15));
}

Rtc::Date parseBeaconFileName(const char* fileName)
{
  String name = String(fileName);
  Rtc::Date result;
  result.day = atoi(name.substring(0,2).c_str());
  result.month = atoi(name.substring(2,4).c_str());
  result.year = atoi(name.substring(4,8).c_str());
  result.hour = atoi(name.substring(9,11).c_str());
  result.minute = atoi(name.substring(11,13).c_str());
  result.second = atoi(name.substring(13,15).c_str());
  return result;
}

void formatFrequencyItem(char* buffer, size_t size, int index, float frequency, bool on)
{
    snprintf(buffer,size,"(%c) %d- %3.4f MHz",on ? '*' : ' ', index+1, frequency);
}

typedef struct {
    float voltage;
    uint8_t percent;
} voltageMap_t;

// Simplified battery discharge curve
typedef struct {
    float relVoltage;   // Relative voltage (from 0.0 to 1.0)
    uint8_t percent;
} battery_point_t;

// Normalized discharge curve
static const battery_point_t batteryCurve[] = {
    {1.00, 100},
    {0.98,  95},
    {0.95,  90},
    {0.90,  80},
    {0.85,  70},
    {0.80,  60},
    {0.75,  50},
    {0.70,  40},
    {0.65,  30},
    {0.60,  20},
    {0.55,  10},
    {0.50,   5},
    {0.00,   0}
};

uint8_t voltageToPercent(float voltage, float voltageMin, float voltageMax) 
{
    if (voltageMax <= voltageMin) return 0;

    // Ratio entre 0.0 (min) et 1.0 (max)
    float norm = (voltage - voltageMin) / (voltageMax - voltageMin);

    const int count = sizeof(batteryCurve) / sizeof(batteryCurve[0]);

    if (norm >= batteryCurve[0].relVoltage) return 100;
    if (norm <= batteryCurve[count - 1].relVoltage) return 0;

    for (int i = 0; i < count - 1; i++) {
        float r_high = batteryCurve[i].relVoltage;
        float r_low  = batteryCurve[i + 1].relVoltage;
        uint8_t p_high = batteryCurve[i].percent;
        uint8_t p_low  = batteryCurve[i + 1].percent;

        if (norm <= r_high && norm >= r_low) 
        {
            float percent = p_low + (norm - r_low) * (p_high - p_low) / (r_high - r_low);
            return (uint8_t)(percent + 0.5f);
        }
    }
    return 0;
}

// String to data conversion helpers
int stringToInt(String stringValue, int defaultVal) 
{
    return stringValue.toInt();
}

bool stringToBool(String stringValue) 
{
    stringValue.trim();
    stringValue.toLowerCase();
    if (stringValue == "true" || stringValue == "1") return true;
    //if (stringValue == "false" || val == "0") return false;
    return false;
}

uint8_t stringToUChar(String stringValue) 
{
    return (uint8_t) stringValue.toInt();
}
// Data to string conversion helpers
String intToString(int value) 
{
    return String(value);
}

String boolToString(bool value) 
{
    return value ? "true" : "false";
}

String ucharToString(uint8_t value) 
{
    return String(value);
}

/* Baudot code matrix */
char BAUDOT_CODE[64]   = {' ','5',' ','9',' ',' ',' ',' ',' ',' ','4',' ','8','0',' ',' ',
                          '3',' ',' ',' ',' ','6',' ','/','-','2',' ',' ','7','1',' ',' ',
                          ' ','T',' ','O',' ','H','N','M',' ','L','R','G','I','P','C','V',
                          'E','Z','D','B','S','Y','F','X','A','W','J',' ','U','Q','K','\0'};


/**
 * Structure for BMP serialization
 */
#pragma pack(push, 1)

struct BMPFileHeader {
  uint16_t bfType;
  uint32_t bfSize;
  uint16_t bfReserved1;
  uint16_t bfReserved2;
  uint32_t bfOffBits;
};

struct BMPInfoHeader {
  uint32_t biSize;
  int32_t  biWidth;
  int32_t  biHeight;
  uint16_t biPlanes;
  uint16_t biBitCount;
  uint32_t biCompression;
  uint32_t biSizeImage;
  int32_t  biXPelsPerMeter;
  int32_t  biYPelsPerMeter;
  uint32_t biClrUsed;
  uint32_t biClrImportant;
};

#pragma pack(pop)

size_t screenshotToBmp(uint8_t* screenBuffer, uint8_t* imageBuffer, size_t width, size_t height)
{
    const uint32_t rowSize = (width * 3 + 3) & ~3; // 4 byte allignement
    const uint32_t imageSize = rowSize * height;
    const uint32_t bmpSize = sizeof(BMPFileHeader) + sizeof(BMPInfoHeader) + imageSize;

    uint8_t *p = imageBuffer;

    BMPFileHeader fh = {
      .bfType = 0x4D42,
      .bfSize = bmpSize,
      .bfReserved1 = 0,
      .bfReserved2 = 0,
      .bfOffBits = sizeof(BMPFileHeader) + sizeof(BMPInfoHeader)
    };

    BMPInfoHeader ih = {
      .biSize = sizeof(BMPInfoHeader),
      .biWidth = (int32_t)width,
      .biHeight = (int32_t)height,
      .biPlanes = 1,
      .biBitCount = 24,
      .biCompression = 0,
      .biSizeImage = imageSize,
      .biXPelsPerMeter = 2835,
      .biYPelsPerMeter = 2835,
      .biClrUsed = 0,
      .biClrImportant = 0
    };

    memcpy(p, &fh, sizeof(fh)); p += sizeof(fh);
    memcpy(p, &ih, sizeof(ih)); p += sizeof(ih);

    // Pixels BMP = BGR + bottom-up
    const uint8_t pad[3] = {0};

    for (int32_t y = height - 1; y >= 0; y--)
    {
      uint8_t *src = screenBuffer + y * width * 3;

      for (uint32_t x = 0; x < width; x++)
      {
        uint8_t b = src[x*3 + 0];
        uint8_t g = src[x*3 + 1];
        uint8_t r = src[x*3 + 2];
        *p++ = b;
        *p++ = g;
        *p++ = r;
      }

      memcpy(p, pad, rowSize - width * 3);
      p += rowSize - width * 3;
    }
    return bmpSize;
}
